meltingrabbit/CanSatForHighSchoolStudents/Arduino/App_LightMeter/README.md

# 実装例 - 明るさ計
## 概要
+ 明るさに応じてサーボが回転し，明るさを差す．
+ [プログラミング講習 10. アプリケーション例](../ProgrammingTutorial10_Application)も参照のこと．

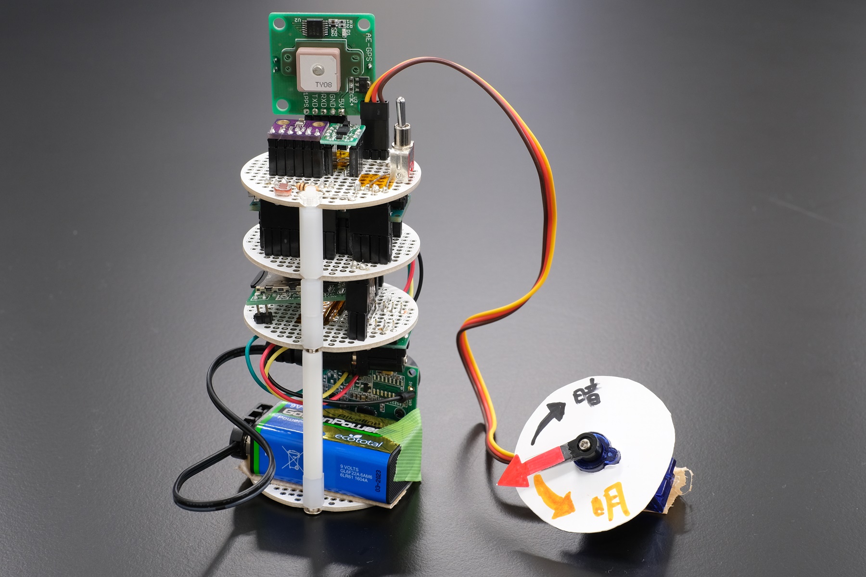
[picture p10: Arduino/App_LightMeter/img/overview.JPG]


## ソースコードへのリンク
[GitHub](https://github.com/meltingrabbit/CanSatForHighSchoolStudents/tree/master/Arduino/App_LightMeter)
