meltingrabbit/CanSatForHighSchoolStudents/Structure/board/README.md

# 構造詳細画像

### Ver.2.1 （2022年版）
バッテリの接続にターミナルブロックを使うことで，DCジャック分の高さを省略するように改良したもの

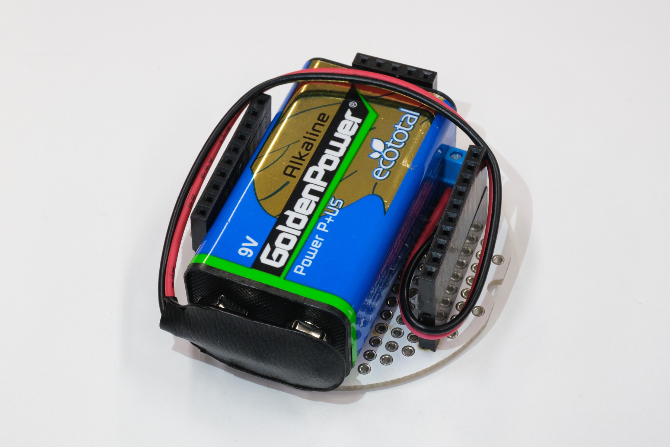
[picture p11: Structure/board/img/2022/battery3.jpg]

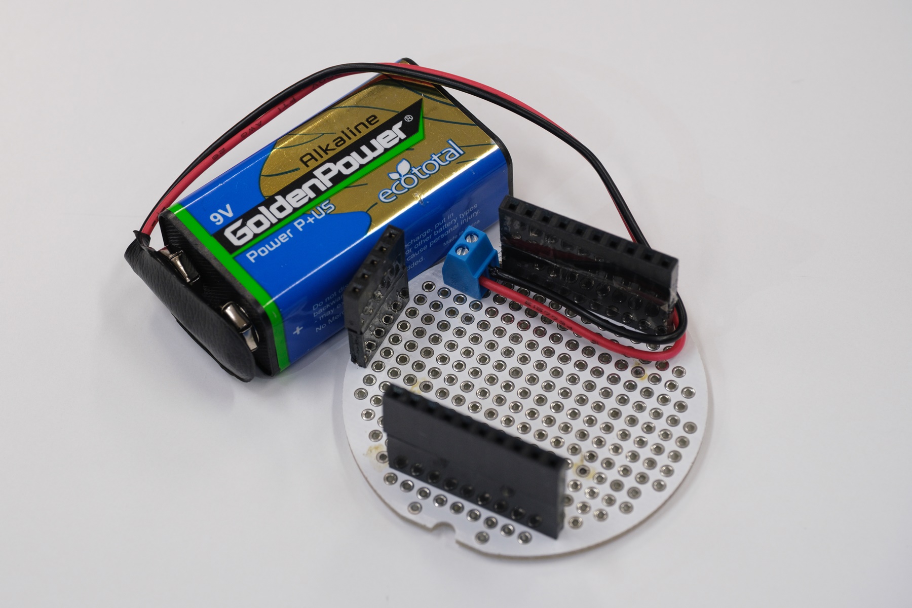
[picture p12: Structure/board/img/2022/battery4.jpg]

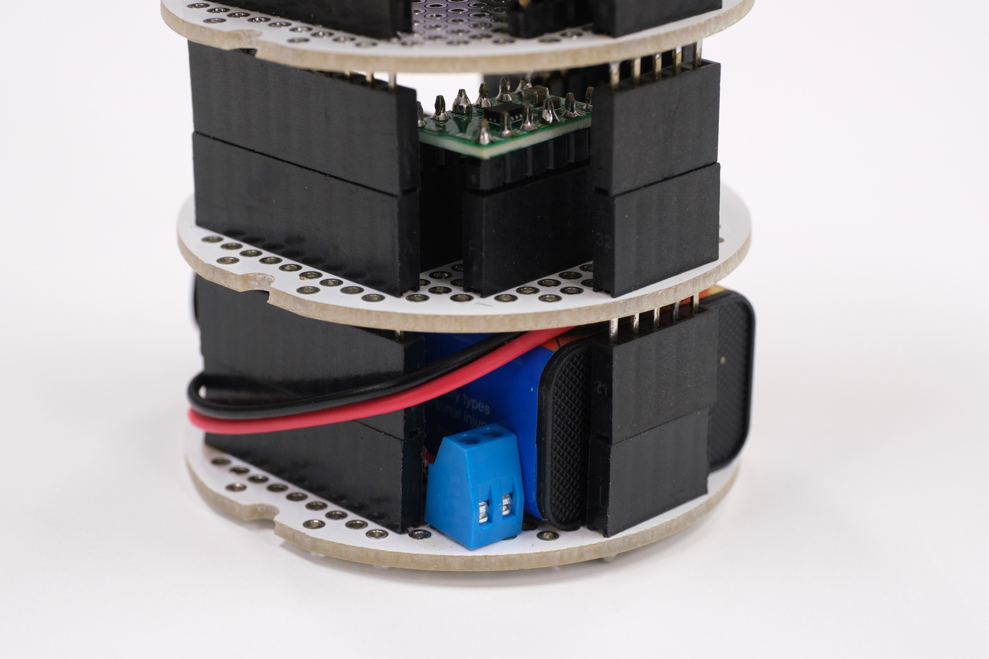
[picture p13: Structure/board/img/2022/battery5.jpg]


### Ver.2 （2021年版）
コアパーツ
- GPS，光，高度計（気圧計），温湿度，電源スイッチ（左）
- XBee（無線機）（中）
- Arduino Nano Every（マイコン）（右）

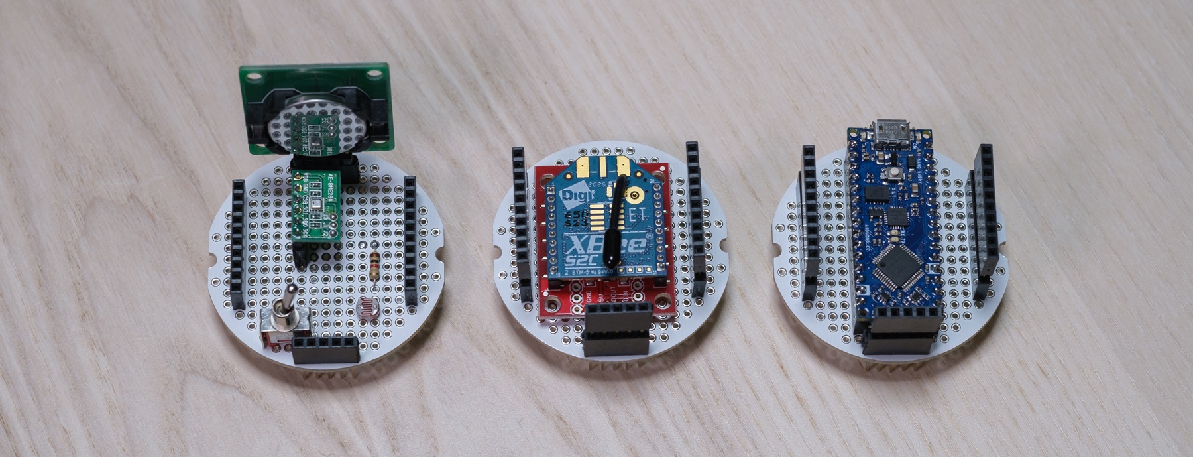
[picture p14: Structure/board/img/2021/core_omote.jpg]

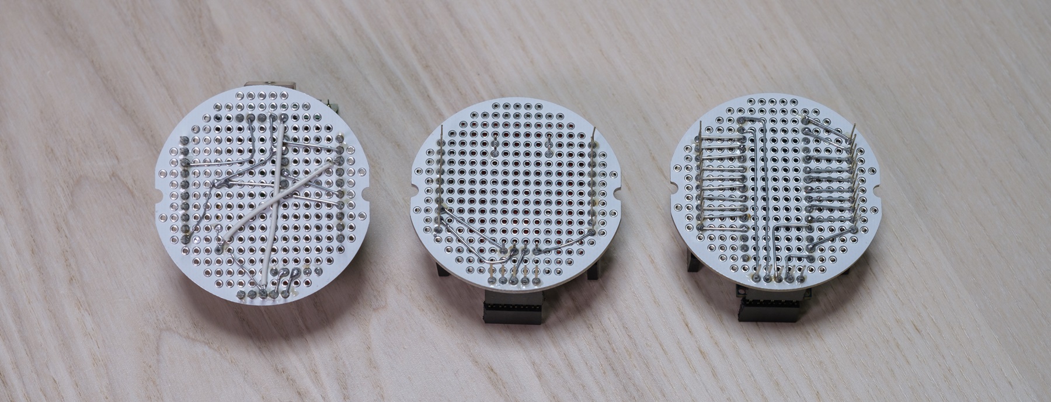
[picture p15: Structure/board/img/2021/core_ura.jpg]


バッテリとサーボモータ
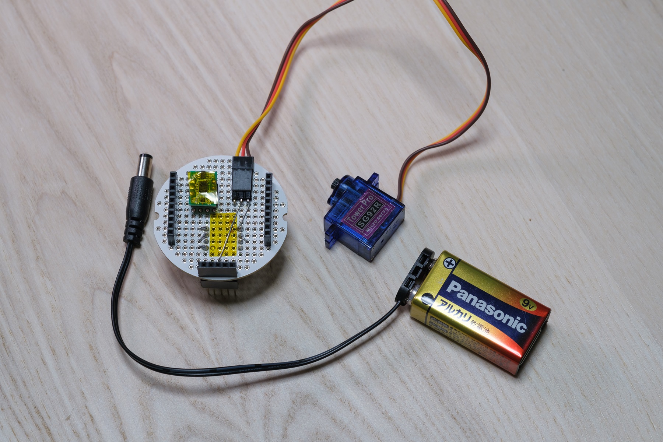
[picture p16: Structure/board/img/2021/battery_omote.jpg]

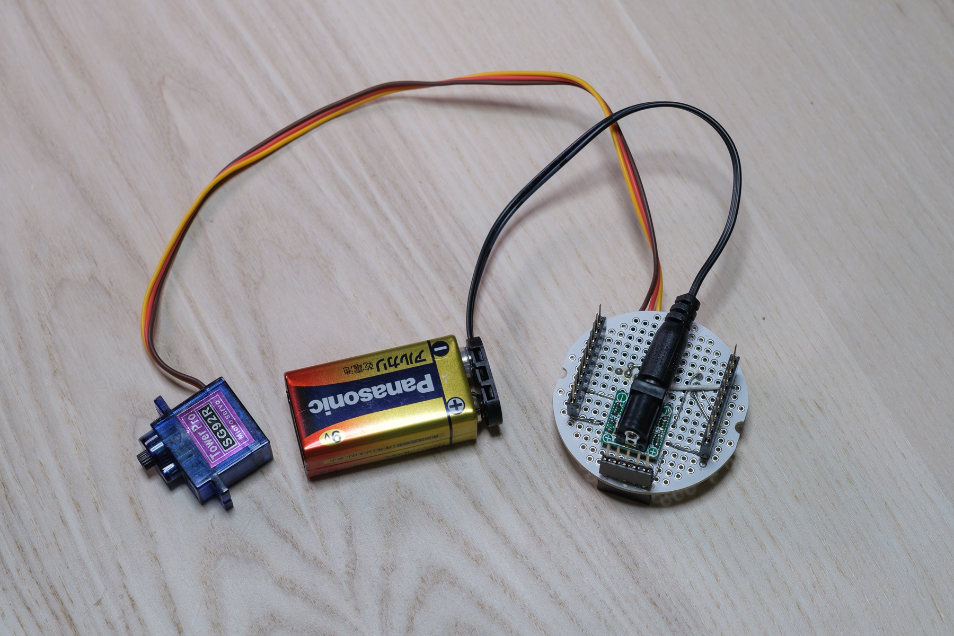
[picture p17: Structure/board/img/2021/battery_ura.jpg]


カメラとSDカード
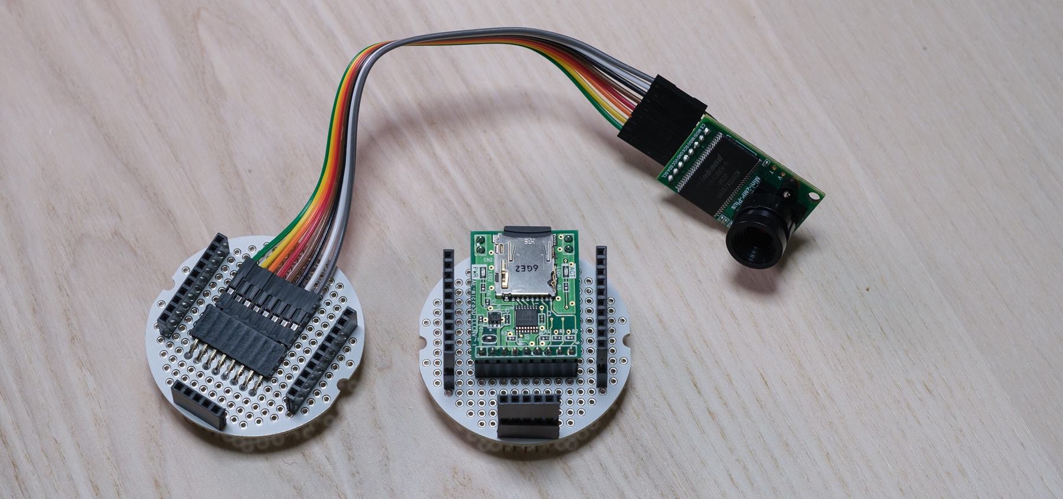
[picture p18: Structure/board/img/2021/camera_omote.jpg]

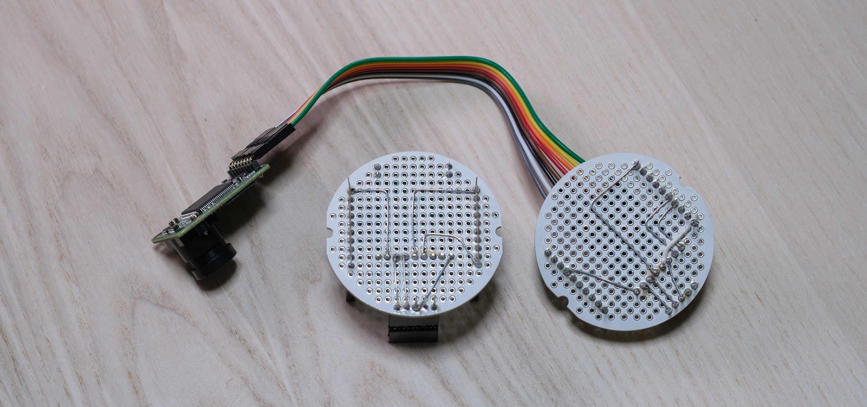
[picture p19: Structure/board/img/2021/camera_ura.jpg]


DCモータと外部電源
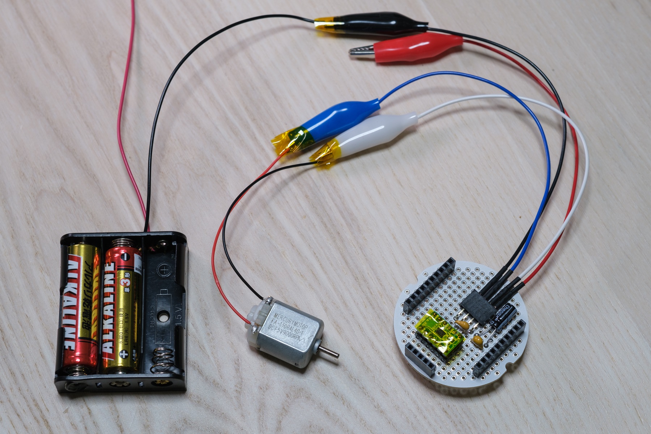
[picture p20: Structure/board/img/2021/dc_moter_omote.jpg]

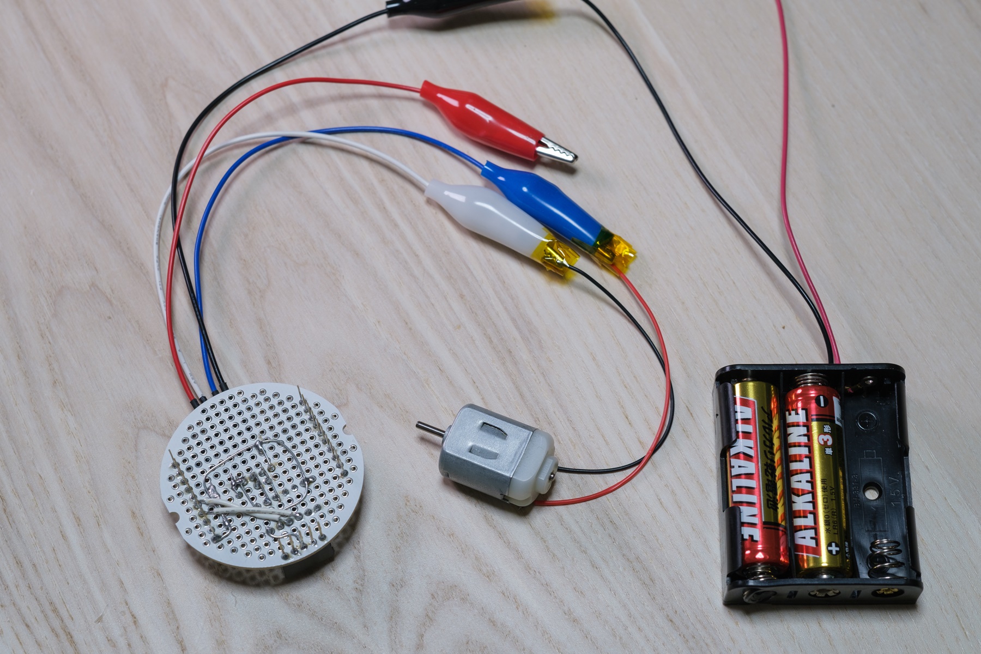
[picture p21: Structure/board/img/2021/dc_moter_ura.jpg]


### Ver.1 （2020年版）
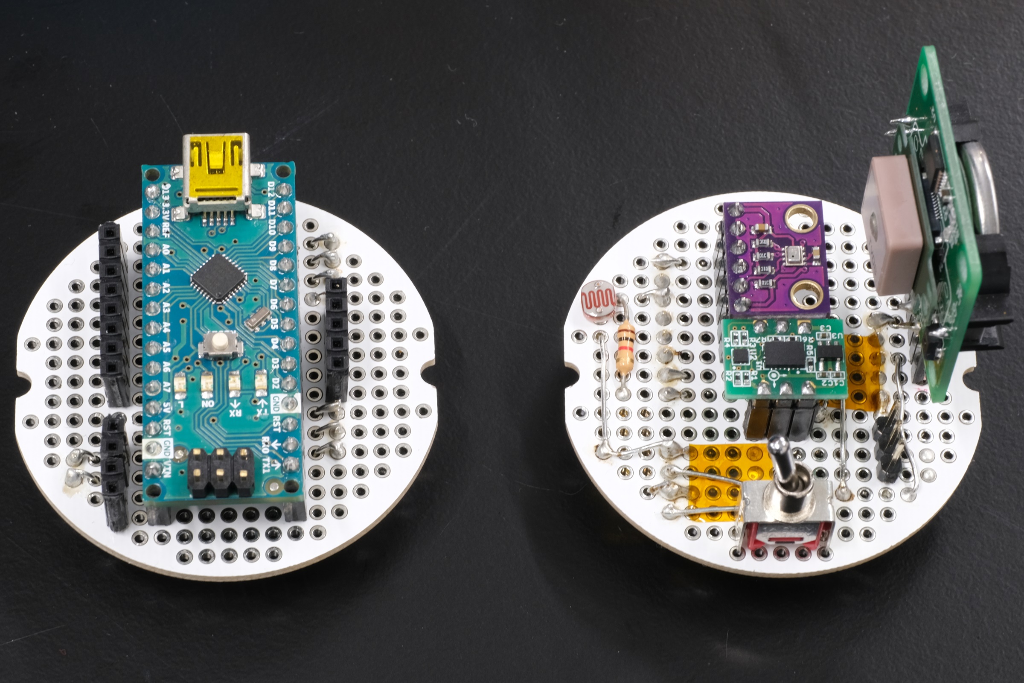
[picture p22: Structure/board/img/2020/top_omote.JPG]

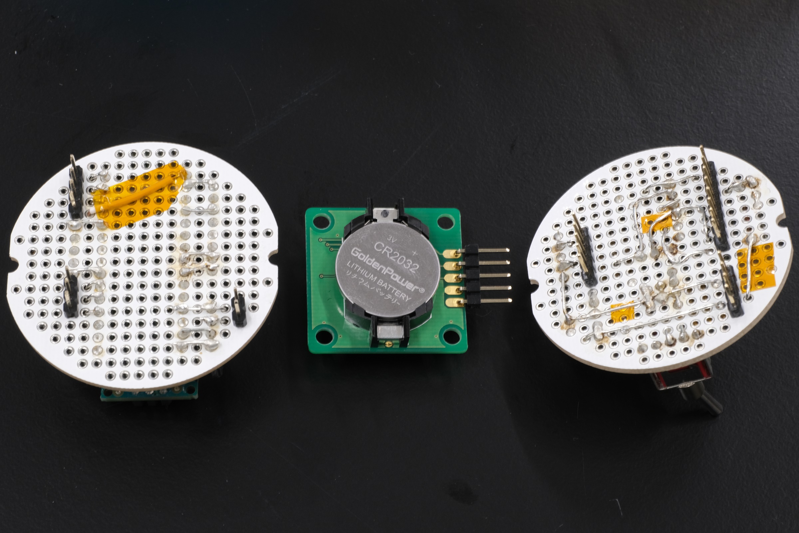
[picture p23: Structure/board/img/2020/top_ura.JPG]

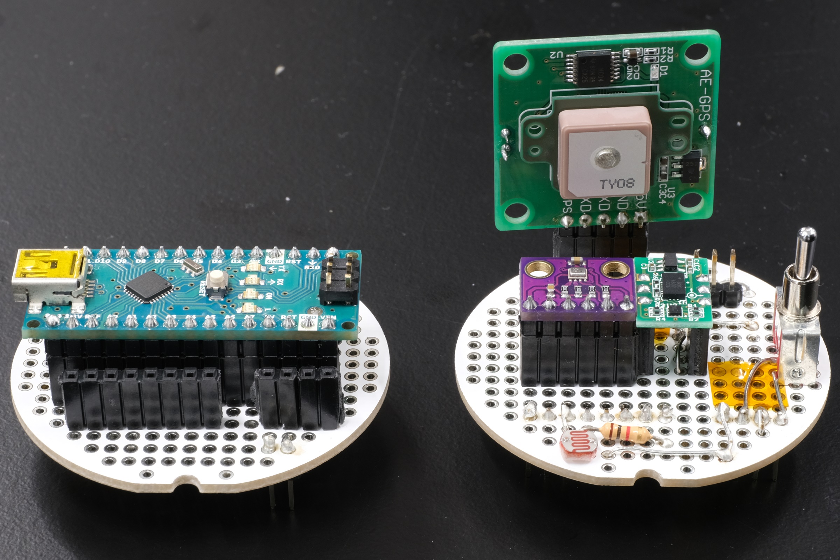
[picture p24: Structure/board/img/2020/top_yoko.JPG]

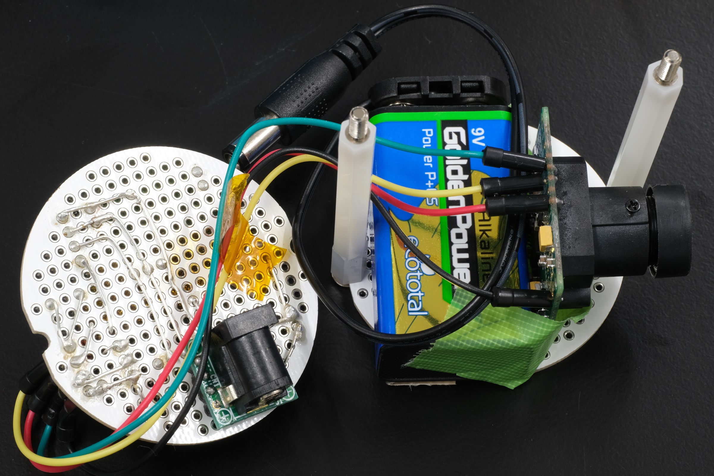
[picture p25: Structure/board/img/2020/bottom_omote.JPG]

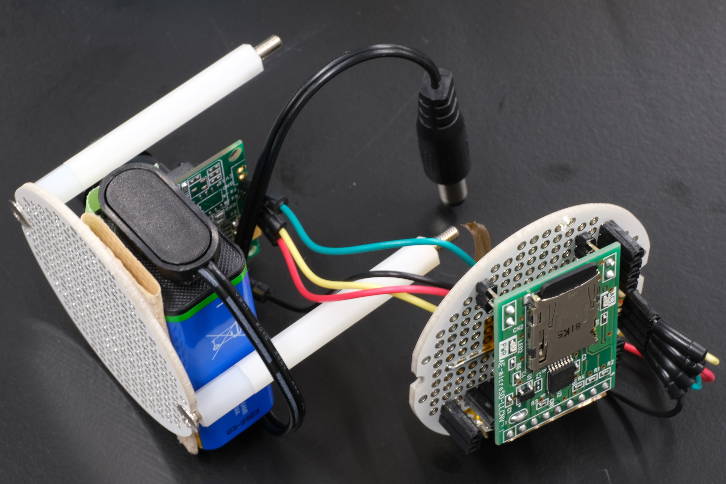
[picture p26: Structure/board/img/2020/bottom_ura.JPG]
