meltingrabbit/CanSatForHighSchoolStudents/Structure/switch/README.md

# 電源スイッチ
## 機器詳細
基板用小型３Ｐトグルスイッチ １回路２接点  
http://akizukidenshi.com/catalog/g/gP-00300/

電極が３本で，倒すと真ん中と端が導通．

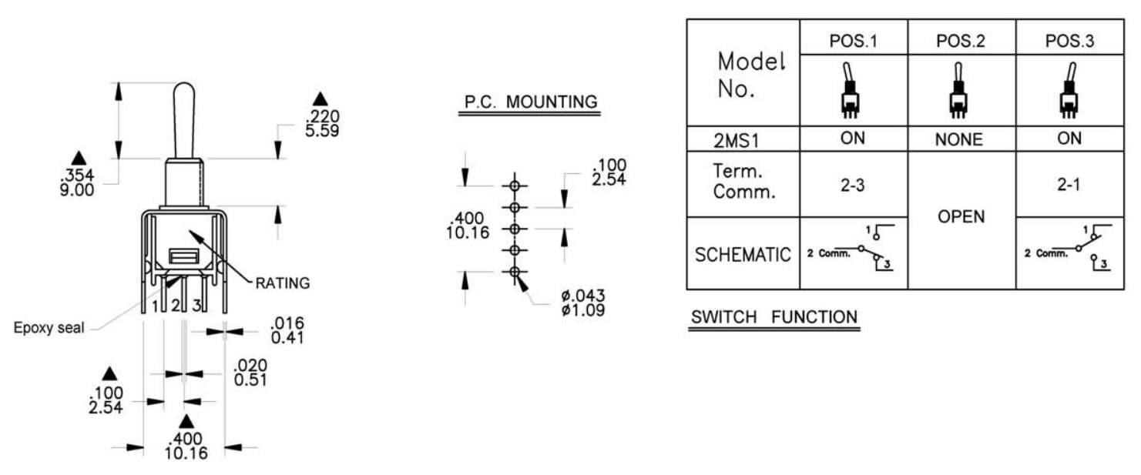
[picture p27: Structure/switch/switch_datasheet.png]


黒と赤が導通
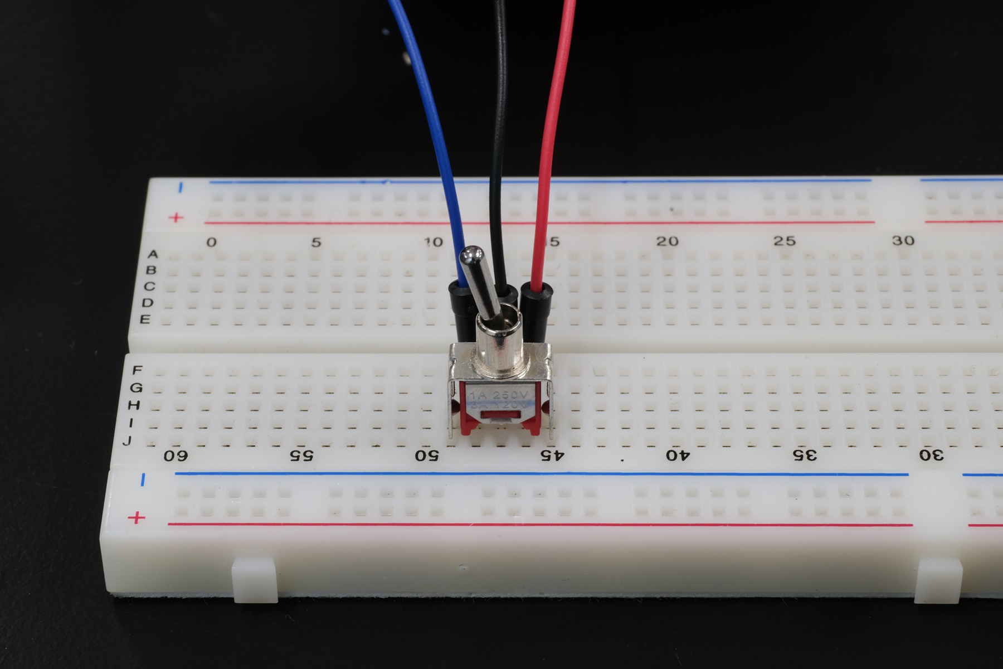
[picture p28: Structure/switch/switch_left.jpg]


黒と青が導通
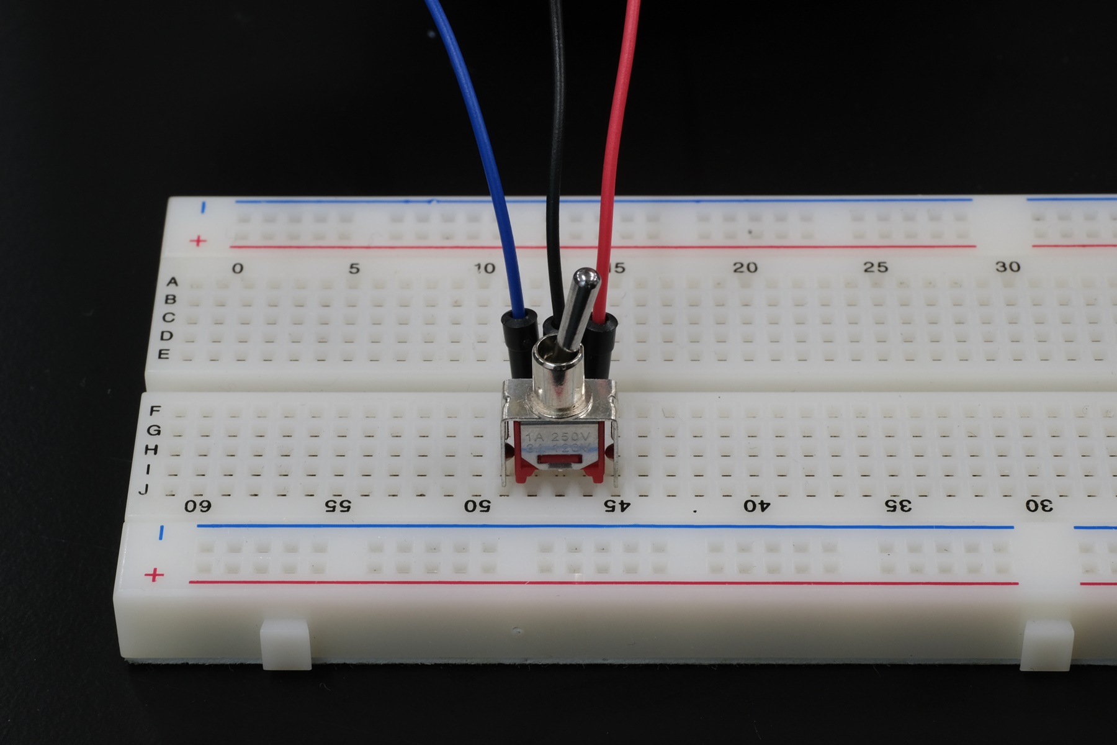
[picture p29: Structure/switch/switch_right.jpg]
