meltingrabbit/CanSatForHighSchoolStudents/Archives/2021-06-19_Fukui/BaseSourceCode/README.md

# 各班が提出してくれたミッションフローチャートを元に作った雛形ソースコード
Sampleは，様々な班につかえるサンプル集．

## ソースコードへのリンク
[GitHub](https://github.com/meltingrabbit/CanSatForHighSchoolStudents/tree/master/Archives/2021-06-19_Fukui/BaseSourceCode)
