meltingrabbit/CanSatForHighSchoolStudents/Archives/2022-03-19_Fukui/Koshi/arduino/README.md

# About

- main
  - 本番使用するコード
- test
  - 各種デバイスの動作確認用

## XBee設定を簡単にまとめてみる

Arduinoがシリアルモニタに送るデータをUSB経由でPCに送っていたのを無線化するためXBeeを使用する
Arduino側をマスター、PC側をスレーブとします

|  | マスター | スレーブ |
| ---- | ---- | ---- |
| ID | 任意 | 任意 |
| DH | 13A200 | 13A200 |
| DL | マスターのSL | マスターのSL |
| CE | Enabled[1] | Disabled[0] |

この状態になるようにいい感じに設定をする
オススメは

- マスターを接続して上記4項目を設定
- ID, SLをどこかにメモる
- PCから取り外し、Arduinoに接続
- スレーブを接続し上記4項目を設定
- コンソールモニタを開いてCloseにし、Arduinoを起動
