meltingrabbit/CanSatForHighSchoolStudents/Archives/2023-02-18_Fukui/README.md

# 2023年02月18～19日 缶サットHigh School 「缶サット電子系講座」
## 各高校のプログラム一覧
+ [藤島](./Fujishima)
+ [金津](./Kanazu)
+ [丸岡](./Maruoka)
+ [三国](./Mikuni)
+ [武生](./Takehu)
+ [敦賀](./Tsuruga)

## ソースコードへのリンク
[GitHub](https://github.com/meltingrabbit/CanSatForHighSchoolStudents/tree/master/Archives/2023-02-18_Fukui)
