meltingrabbit/CanSatForHighSchoolStudents/Archives/2022-03-19_Fukui/README.md

# 2022年03月19～20日 缶サットHigh School 「缶サット電子系講座」
## 各高校のプログラム一覧
+ [藤島](./Fujishima)
+ [科学技術](./Kagakugijutsu)
+ [高志](./Koshi)
+ [鯖江](./Sabae)
+ [武生東](./TakefuHigashi)
+ [若狭](./Wakasa)

## ソースコードへのリンク
[GitHub](https://github.com/meltingrabbit/CanSatForHighSchoolStudents/tree/master/Archives/2022-03-19_Fukui)
