meltingrabbit/CanSatForHighSchoolStudents/Archives/2021-06-19_Fukui/README.md

# 2021年06月19～20日 缶サットHigh School 「缶サット構造系講座」
+ [各班に配布した，雛形プログラム](./BaseSourceCode)
+ [当日の実装結果](./Result)

## ソースコードへのリンク
[GitHub](https://github.com/meltingrabbit/CanSatForHighSchoolStudents/tree/master/Archives/2021-06-19_Fukui)
