meltingrabbit/CanSatForHighSchoolStudents/Archives/2020-02-22_Fukui/README.md

# 2020年02月22～23日 缶サットHigh School 「缶サット電子系講座」
## 各高校のプログラム一覧
+ [01班 武生東](./01_Takefuhigashi)
+ [02班 敦賀A](./02_TsurugaA)
+ [03班 敦賀B](./03_TsurugaB)
+ [04班 藤島](./04_Fujishima)
+ [05班 高志](./05_Koshi)
+ [06班 三国](./06_Mikuni)
+ [07班 科学技術](./07_Kagakugijutsu)
+ [08班 武生工業](./08_Takefukougyou)
+ [09班 武生](./09_Takefu)
+ [10班 福井工業大学附福井](./10_Fukuikougyoudaigakufukui)
+ [11班 若狭](./11_Wakasa)

## ソースコードへのリンク
[GitHub](https://github.com/meltingrabbit/CanSatForHighSchoolStudents/tree/master/Archives/2020-02-22_Fukui)
