meltingrabbit/CanSatForHighSchoolStudents/Schematic/PNG/Camera2.png

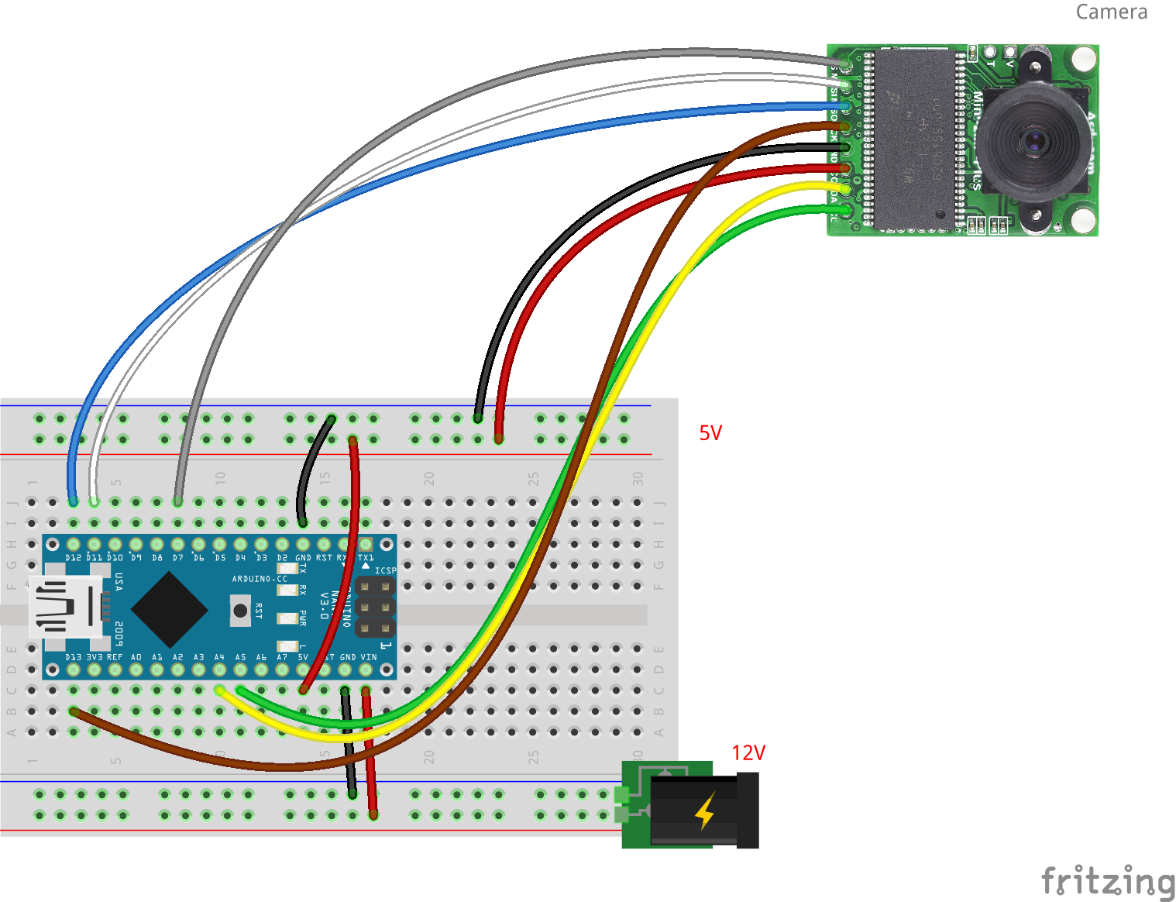
Schematic/PNG/Camera2.png
