meltingrabbit/CanSatForHighSchoolStudents/Schematic/PNG/Camera2x2_SD.png

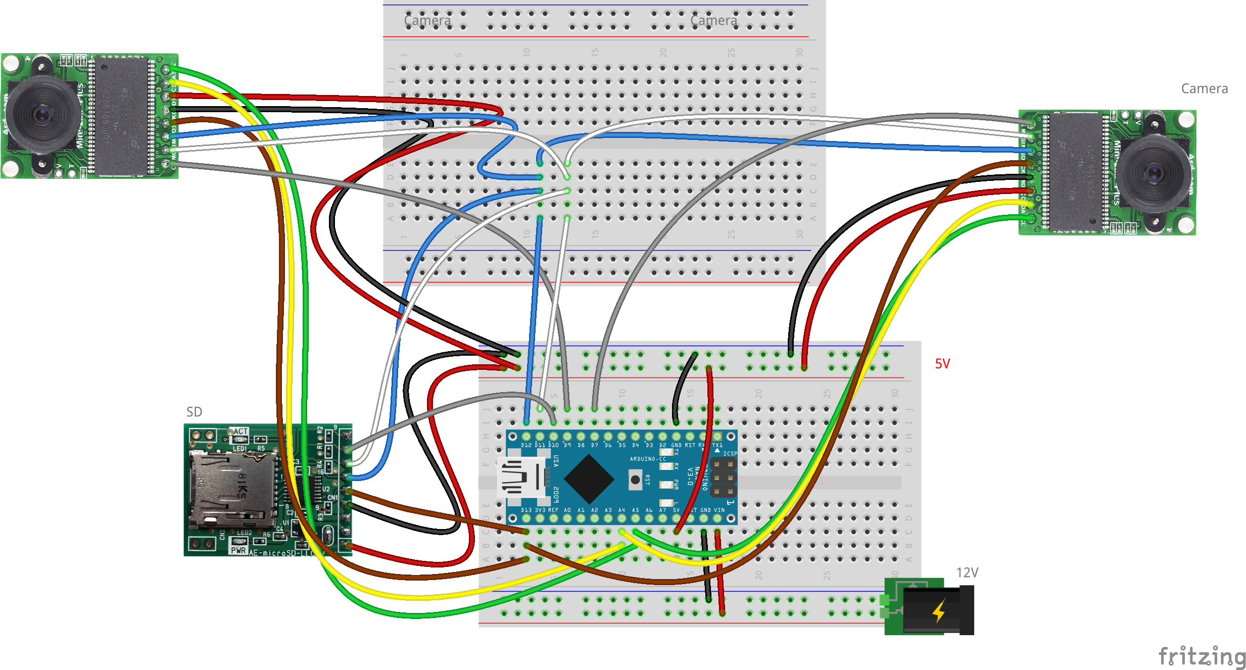
Schematic/PNG/Camera2x2_SD.png
