meltingrabbit/CanSatForHighSchoolStudents/Schematic/PNG/Camera.png

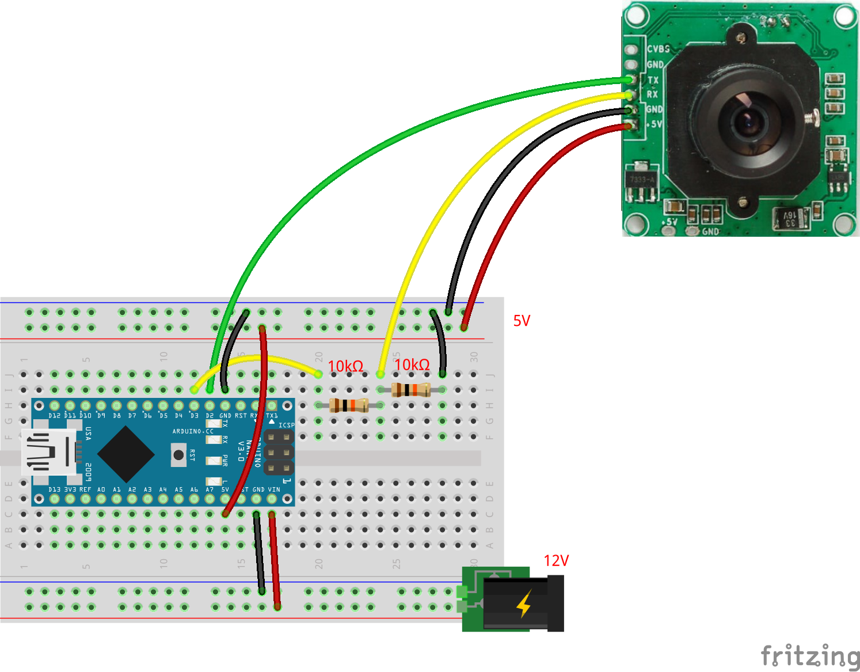
Schematic/PNG/Camera.png
