meltingrabbit/CanSatForHighSchoolStudents/Structure/img/2020/board_top.jpg

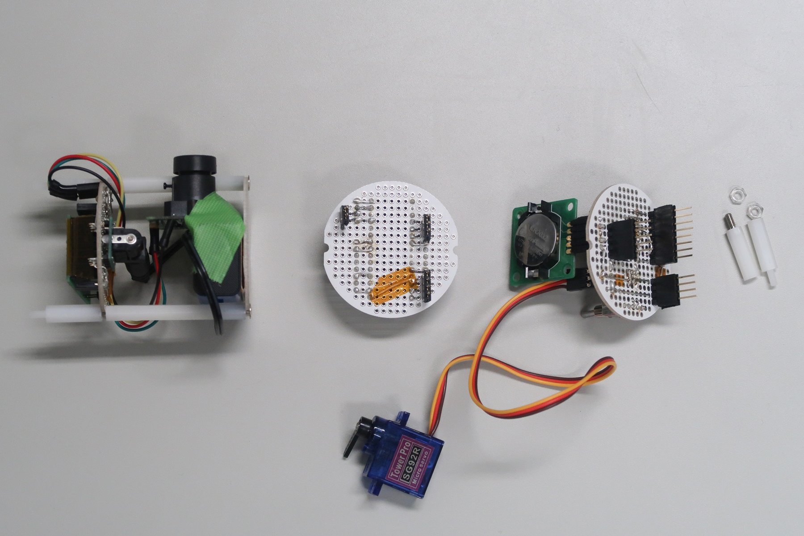
Structure/img/2020/board_top.jpg
