meltingrabbit/CanSatForHighSchoolStudents/Arduino/Test_Barometer/README.md

# 気圧計の単体テストコード
## 概要
気圧計の単体テストコード  
温度も取得可能  
気圧から高度が計算できる

メモリ節約のため，ライブラリは未使用  
（[Adafruitのライブラリ使用版](../Test_Barometer_with_lib/README.md)）

## 機器詳細
気圧センサ GY-BMP280-3.3  
https://www.led-paradise.com/product/2334

## 回路図
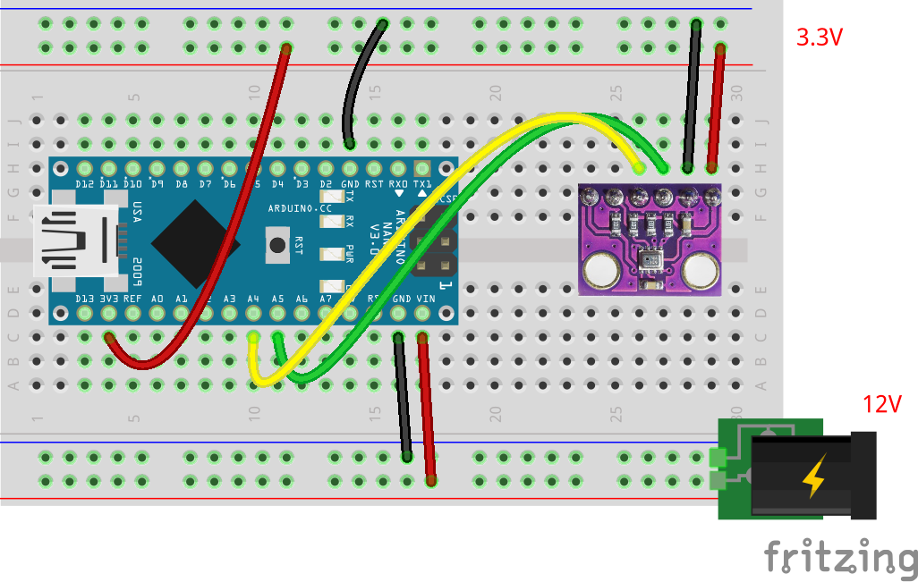
[picture p43: Schematic/PNG/Barometer.png]


| 素子 Pin | Arduino Pin | 備考 |
| ---- | ---- | ---- |
| VCC | 3V3 | 3.3V 電源 |
| GND | GND | GND |
| SCL | A5 (SCL) | I2C のシリアルクロック |
| SDA | A4 (SDA) | I2C のシリアルデータ |
| CSB | - | ここでは未使用（未接続） |
| SDO | - | ここでは未使用（未接続） |

+ 通信はI2C
+ 電圧は3.3V
	- I2Cの信号線は，レベル変換を挟むとなお良い

## ソースコードへのリンク
[GitHub](https://github.com/meltingrabbit/CanSatForHighSchoolStudents/tree/master/Arduino/Test_Barometer)
