meltingrabbit/CanSatForHighSchoolStudents/Structure/tester/README.md

# テスタ
+ はんだ付けなどがうまくいって，導通しているかを確認できる．
+ スピーカのマークにダイヤルを合わせ，電極をつけると，導通しているときにのみ，ビープ音が鳴る．
