meltingrabbit/CanSatForHighSchoolStudents/Archives/2021-06-19_Fukui/Result/README.md

# 当日の実装結果
## ソースコード
各フォルダに

## 機体
### 丸岡
  

### 敦賀
 

### 武生東
 

### 科学技術
  

### 藤島
 

### 高志中
 

### 高志高
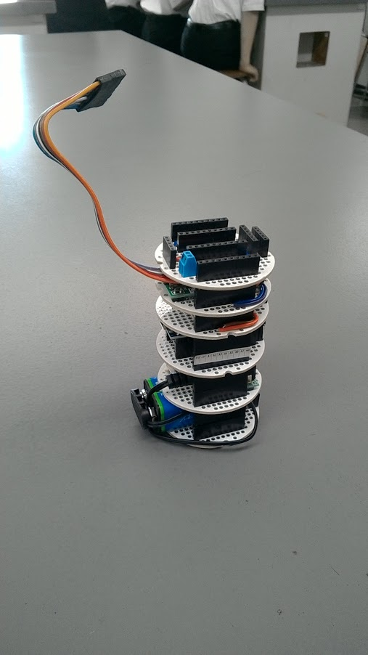
[picture p60: Archives/2021-06-19_Fukui/Result/img/高志高 (1).jpg]
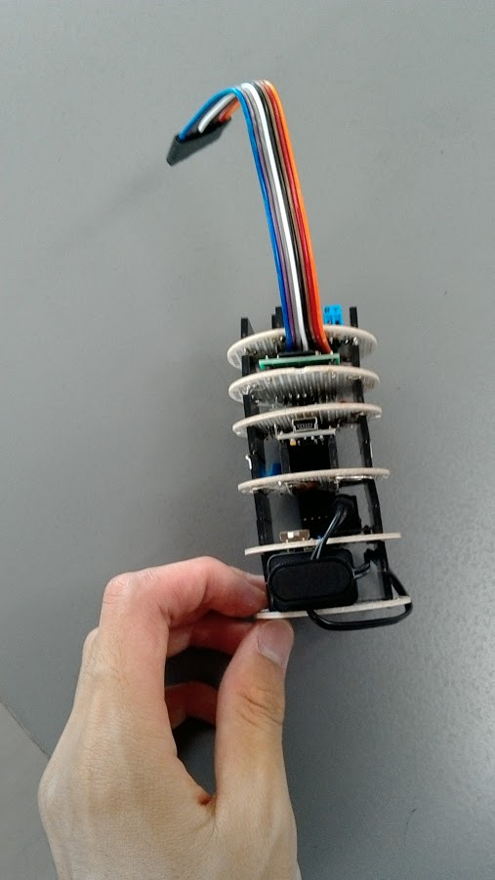
[picture p61: Archives/2021-06-19_Fukui/Result/img/高志高 (2).jpg]
 

### 鯖江
 

## ソースコードへのリンク
[GitHub](https://github.com/meltingrabbit/CanSatForHighSchoolStudents/tree/master/Archives/2021-06-19_Fukui/Result)
