meltingrabbit/CanSatForHighSchoolStudents/Archives/2022-03-19_Fukui/Koshi/arduino/test/GPS/README.md

# 注意点等

このテストコードは`SoftWareSerial` と`TinyGPS` のライブラリを使用しています。忘れずにインストールしておいて下さい
