meltingrabbit/CanSatForHighSchoolStudents/Schematic/PDF/Camera2_SD.pdf

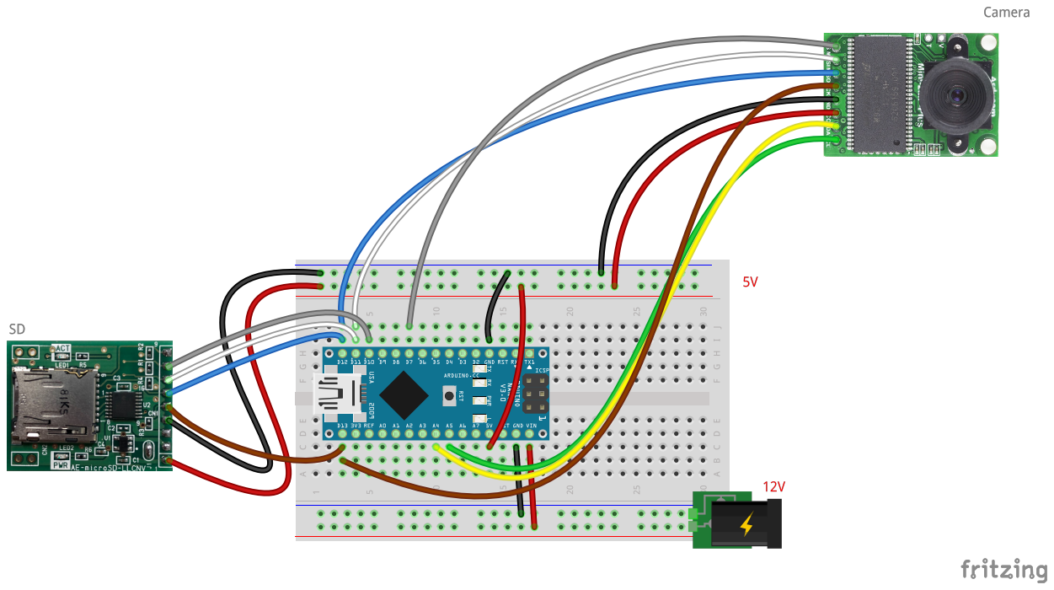
[picture p74: page 1]
