meltingrabbit/CanSatForHighSchoolStudents/Schematic/PDF/Light.pdf

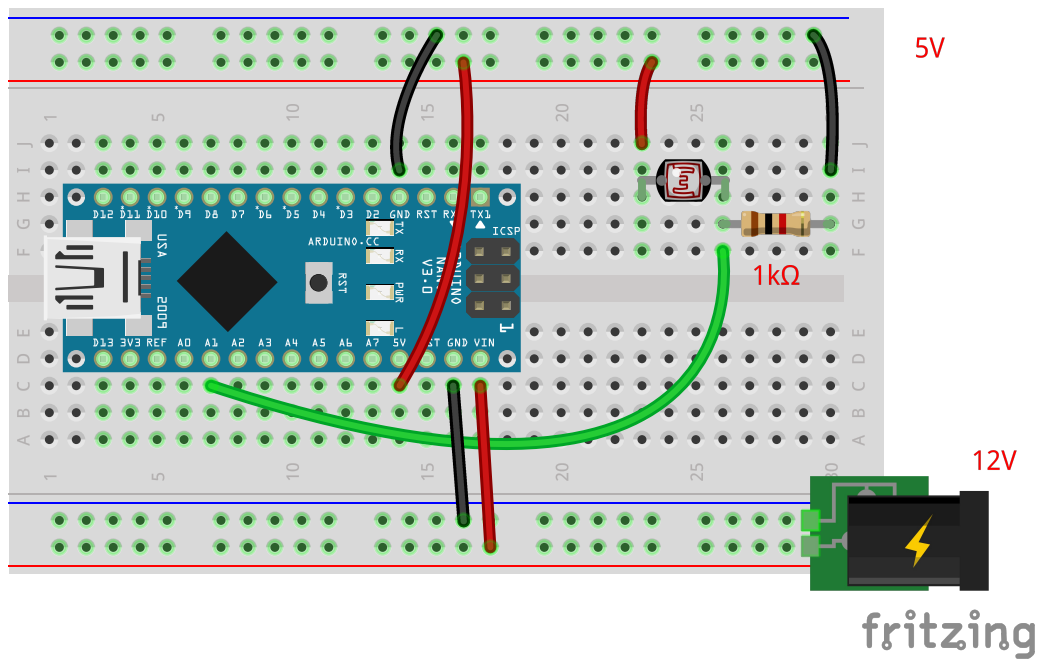
[picture p75: page 1]
