meltingrabbit/CanSatForHighSchoolStudents/Schematic/PDF/IMU.pdf

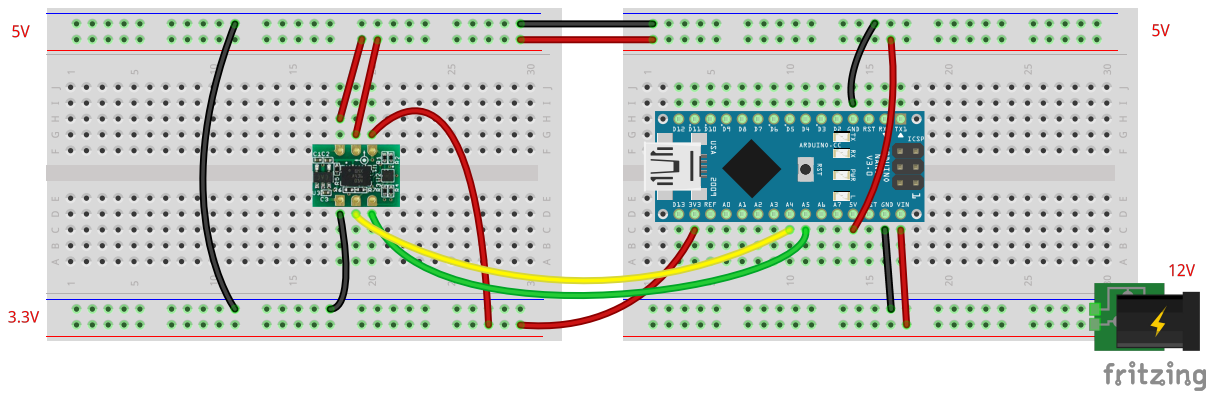
[picture p76: page 1]
