meltingrabbit/CanSatForHighSchoolStudents/Schematic/PDF/Servo.pdf

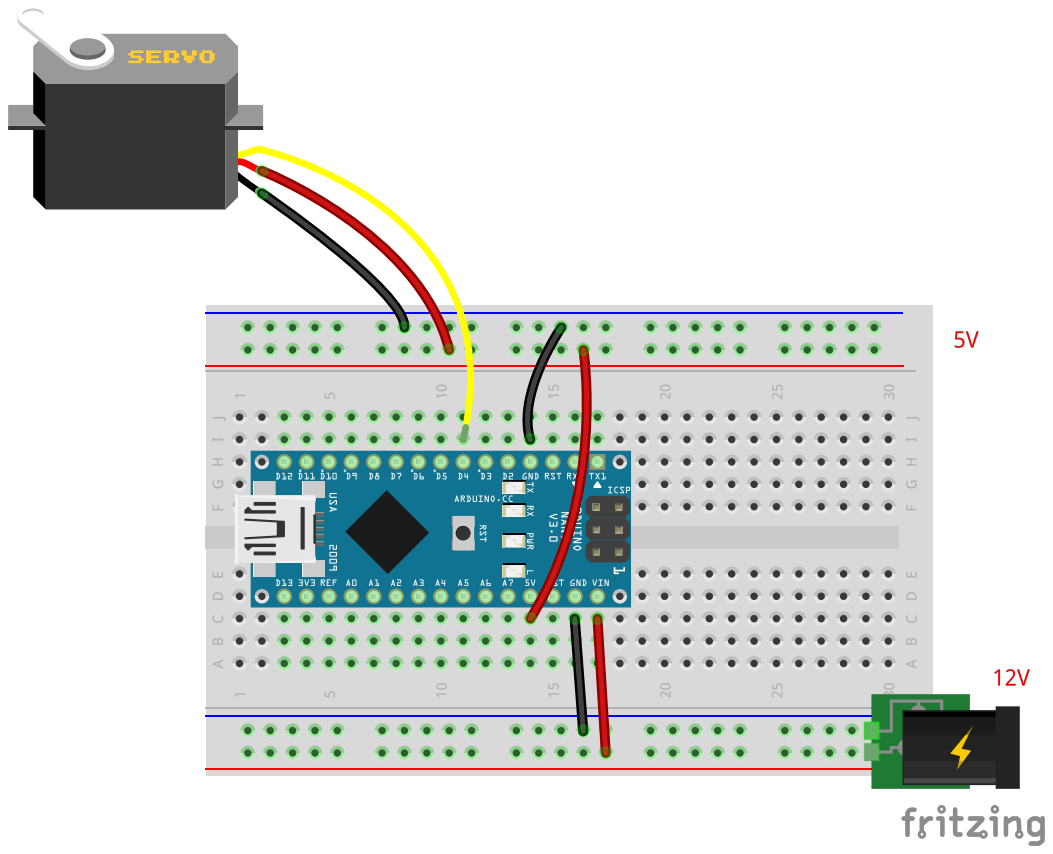
[picture p77: page 1]
