meltingrabbit/CanSatForHighSchoolStudents/Schematic/PDF/Barometer.pdf

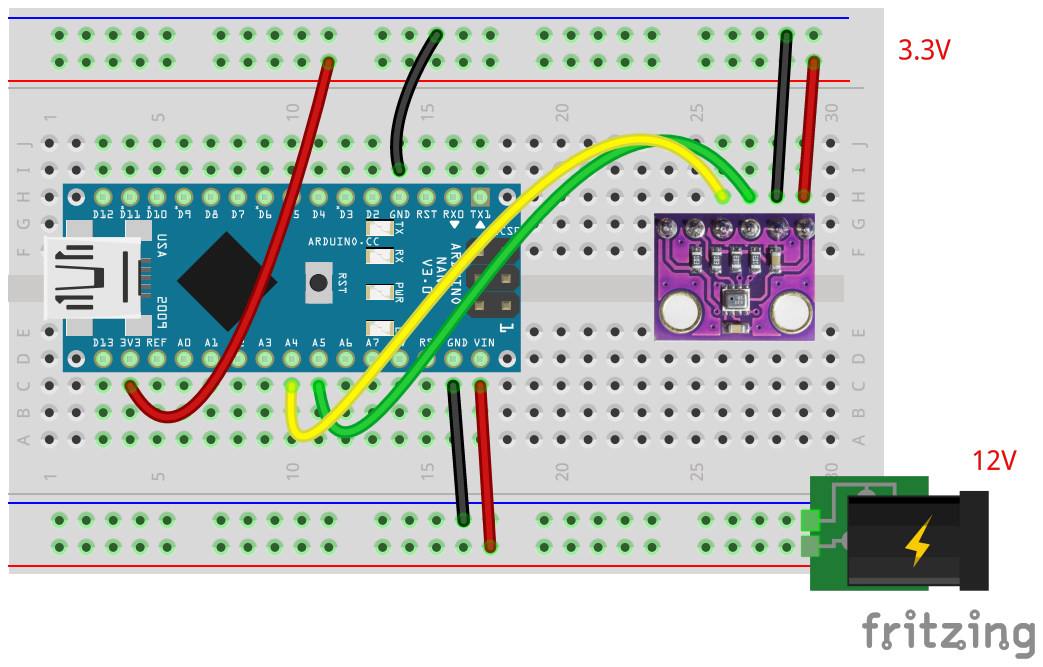
[picture p78: page 1]
