meltingrabbit/CanSatForHighSchoolStudents/Schematic/PDF/Camera.pdf

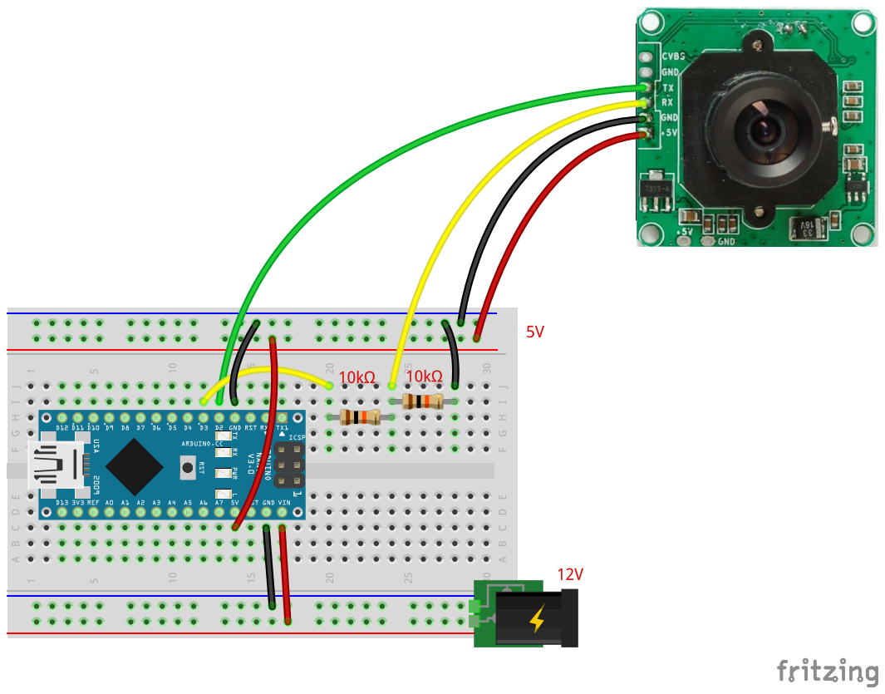
[picture p79: page 1]
