meltingrabbit/CanSatForHighSchoolStudents/Schematic/PDF/GPS.pdf

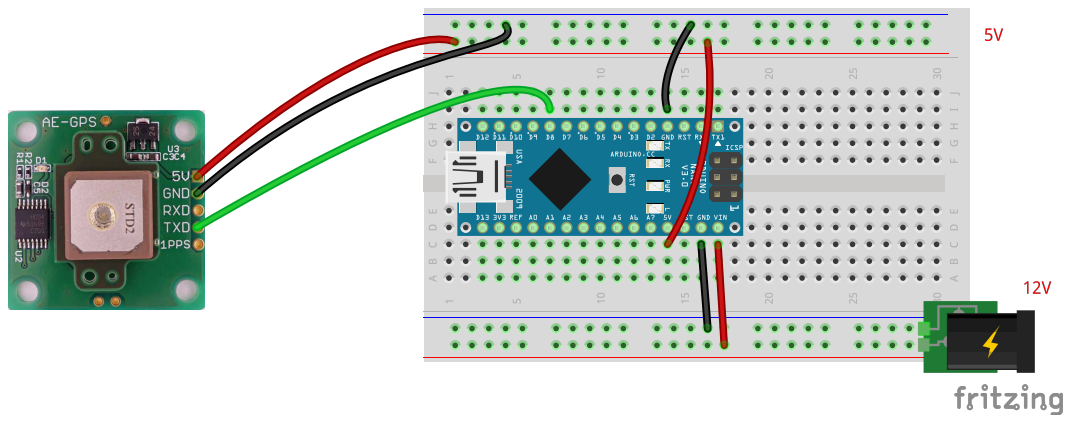
[picture p80: page 1]
