meltingrabbit/CanSatForHighSchoolStudents/Arduino/ProgrammingTutorial08_Device2/PIN_ASSIGN.h

#ifndef PIN_ASSIGN_H
#define PIN_ASSIGN_H

#define PIN_SRV 4

#define PIN_LIT A1
#define PIN_MIC A2

#define PIN_GPS_TX 8
#define PIN_GPS_RX 9
#define PIN_XBEE_TX 2
#define PIN_XBEE_RX 3
#define PIN_SD_SS  10
// SD MOSI 11
// SD MISO 12
// SD CLK  13

#define PIN_CAM2_SS 7

#define PIN_DC_MOTER1 5
#define PIN_DC_MOTER2 6

// #define SDA A4
// #define SCL A5

#endif
