meltingrabbit/CanSatForHighSchoolStudents/Arduino/Test_Light_x4/PIN_ASSIGN.h

#ifndef PIN_ASSIGN_H
#define PIN_ASSIGN_H


#define PIN_SRV 4

#define PIN_LIT A0
#define PIN_LIT2 A1
#define PIN_LIT3 A2
#define PIN_LIT4 A3

#define PIN_GPS_TX 8
#define PIN_GPS_RX 9
#define PIN_SD_SS  10
// SD MOSI 11
// SD MISO 12
// SD CLK  13

#define PIN_CAM_TX 2
#define PIN_CAM_RX 3

#define PIN_SW 5


// #define SDA A4
// #define SCL A5


#endif
