meltingrabbit/CanSatForHighSchoolStudents/Arduino/Test_Barometer/Test_Barometer.ino

#include "./Barometer.h"

void setup()
{
	// Wire(Arduino-I2C)の初期化
	Wire.begin();
	// デバック用シリアル通信は9600bps
	Serial.begin(9600);

	// 初期化
	BMP_Init();

	Serial.println(F("Init done"));
	delay(300);
}

void loop()
{

	BMP_Update();		// 気圧の値をアップデート
	BMP_Print();		// アップデートした値を表示

	delay(1000);		// 1000 ms 待つ
}
